victorlucachi/void9/Redux/STL/Controller/36x18mm - Type C Pro Micro - Flat.stl

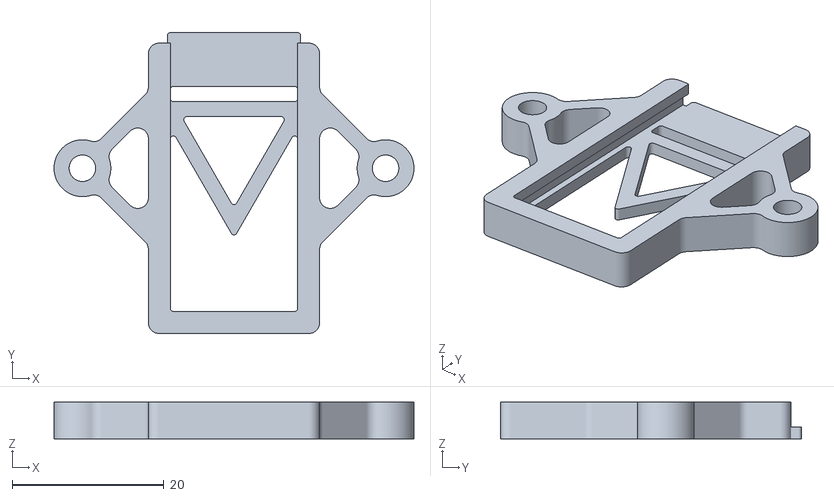
[picture p15: CAD file, 2023-06-13]
Redux/STL/Controller/36x18mm - Type C Pro Micro - Flat.stl
47.5 x 39.7 x 4.86
