victorlucachi/void9/Redux/STL/Controller/33x18mm - Pro Micro - Angled.stl

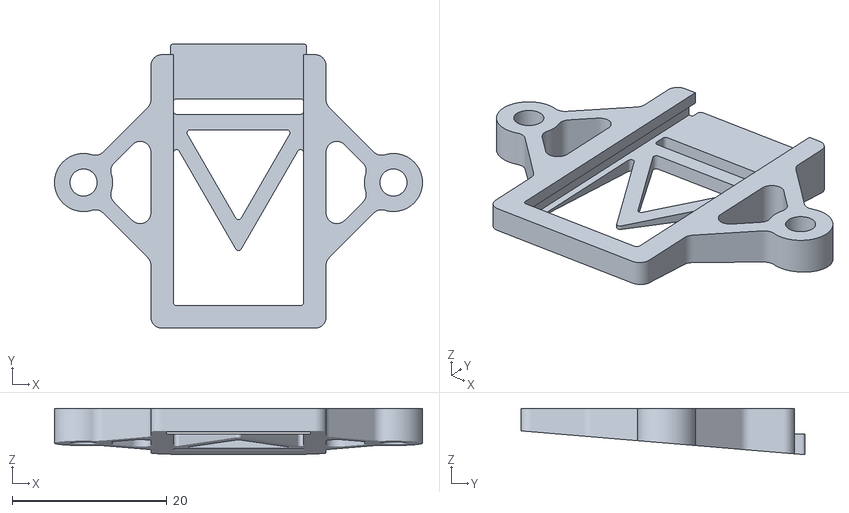
[picture p16: CAD file, 2023-06-13]
Redux/STL/Controller/33x18mm - Pro Micro - Angled.stl
47.5 x 36.7 x 6.00
